stickteo/HipHopAmp/kicad/hopamp/hopamp.png

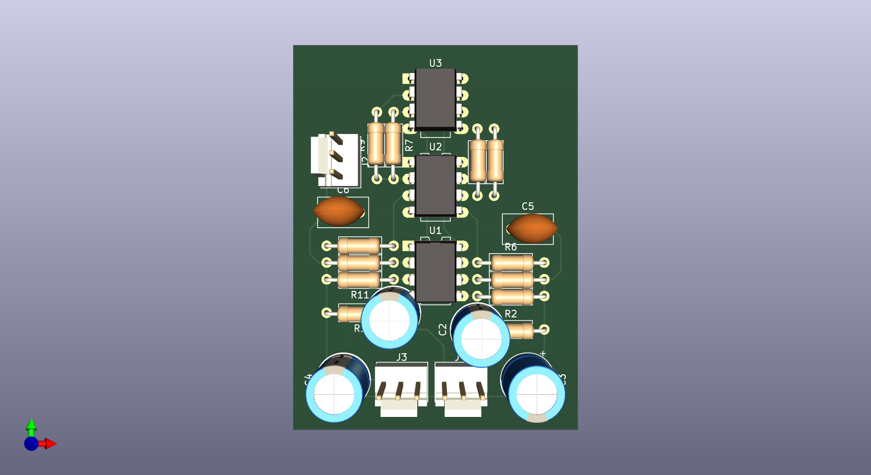
kicad/hopamp/hopamp.png
