stickteo/HipHopAmp/kicad/hopamp/hopamp_front.png

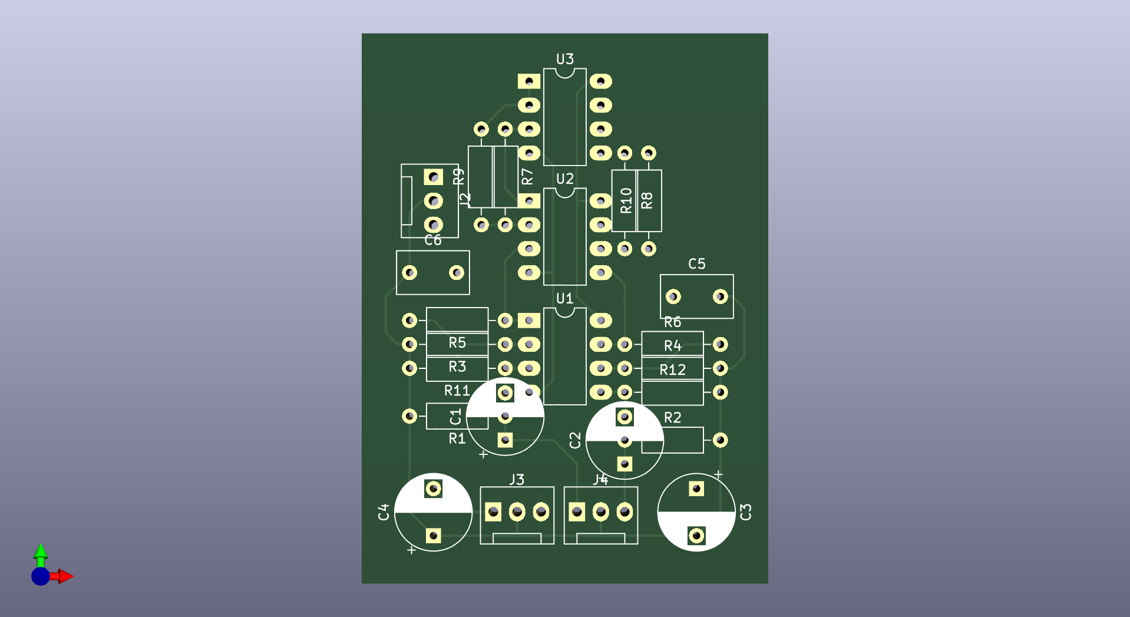
kicad/hopamp/hopamp_front.png
